mattdibi/redox-keyboard/img/redox-layout-1.1.png

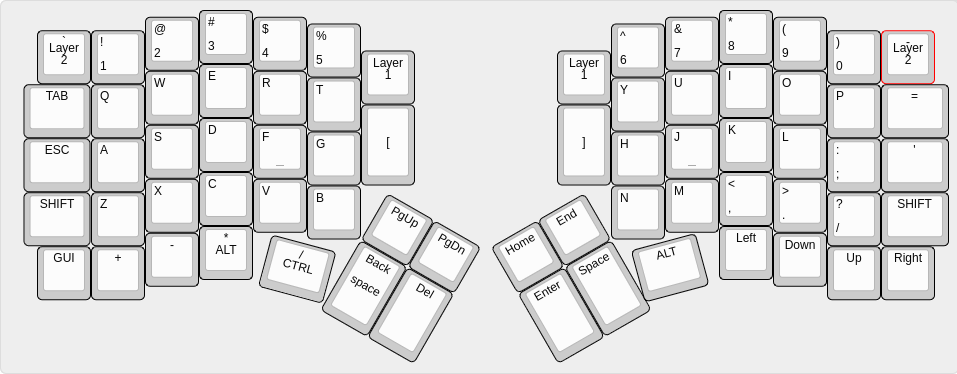
img/redox-layout-1.1.png
