mattdibi/redox-keyboard/img/Switch-location.PNG

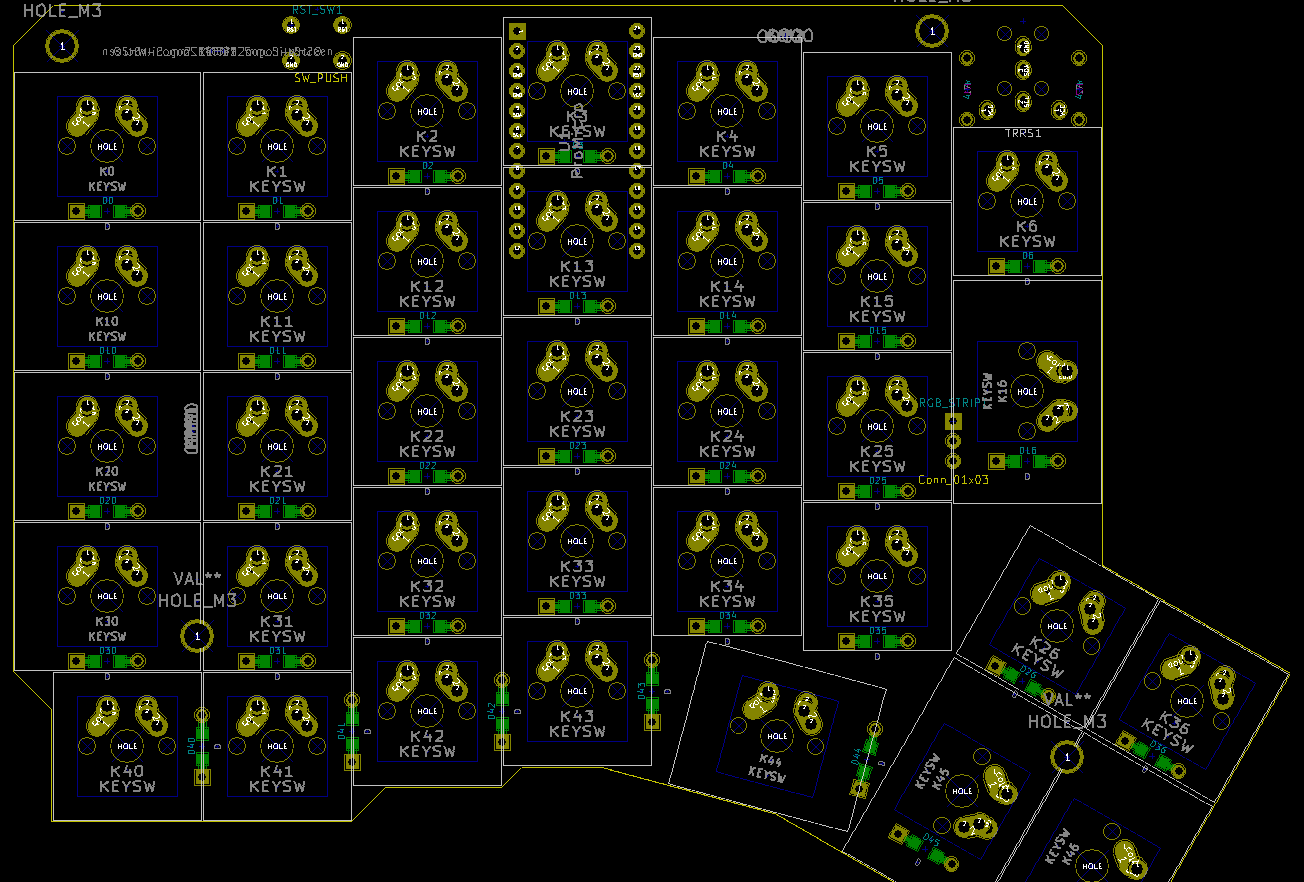
img/Switch-location.PNG
